savannahdevoe/BRPTGuide/CAD_3DPrinting/PCB.SLDPRT

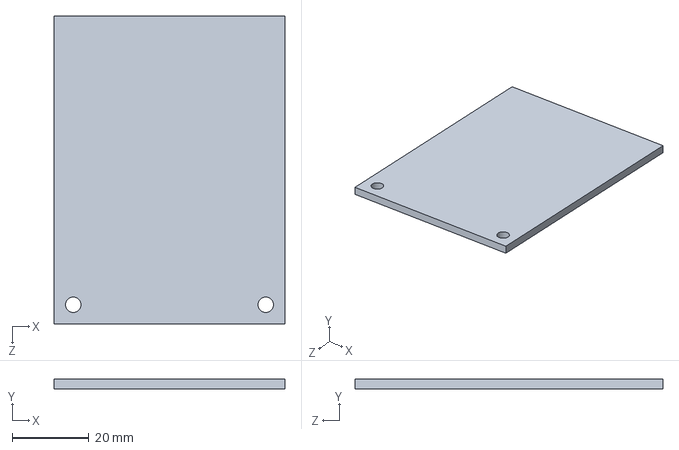
[picture p15: CAD file, 2023-04-27]
CAD_3DPrinting/PCB.SLDPRT
60.0 x 2.54 x 80.0 mm
