savannahdevoe/BRPTGuide/CAD_3DPrinting/3in series end cap 3 holes.SLDPRT

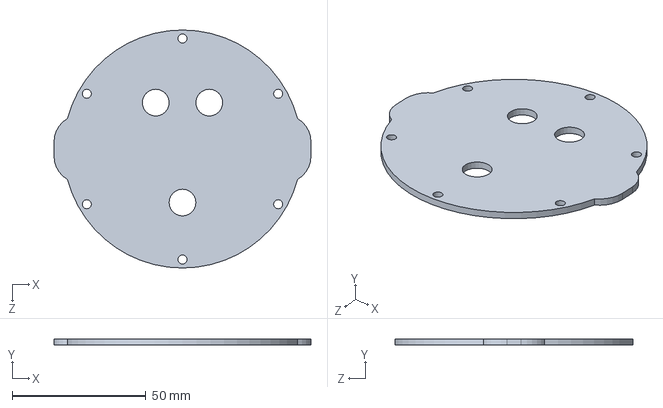
[picture p16: CAD file, 2023-04-27]
CAD_3DPrinting/3in series end cap 3 holes.SLDPRT
96.0 x 2.40 x 88.9 mm
